Diplomatic-Entertainment/JustAnotherCartridgeReader/Firmware/FLASH_CPS3.ino

//******************************************
// CP System III Module
// Cartridge
// 32/64/128 Mbits SIMM
// Tested with  HW5
// https://github.com/herzmx/CPS3-OSCR-Adapter
//******************************************
#if (defined(ENABLE_CPS3) && defined(ENABLE_FLASH8) && defined(ENABLE_FLASH16))
/******************************************
   Variables
 *****************************************/
uint32_t cartRegion = 0;
uint32_t cartCD = 0;
uint32_t cartCDPatch = 0;
uint32_t multiCart = 0;
uint32_t multiCartPatch1 = 0;
uint32_t multiCartPatch2 = 0;
uint32_t cartRegionOffset = 0;
uint32_t cartnocdOffset = 0;
uint16_t flashids[8];

/******************************************
   Menu
 *****************************************/
// CPS3 start menu options
static const char cpsMenuItem1[] PROGMEM = "CPS3 cartridge";
static const char cpsMenuItem2[] PROGMEM = "32/128 Mbits SIMM";
static const char cpsMenuItem3[] PROGMEM = "64 Mbits SIMM";
static const char cpsMenuItem4[] PROGMEM = "32/128 MBytes SIMM";
static const char cpsMenuItem5[] PROGMEM = "64 MBytes SIMM";
static const char* const menuOptionsCPS[] PROGMEM = { cpsMenuItem1, cpsMenuItem2, cpsMenuItem3, cpsMenuItem4, cpsMenuItem5, FSTRING_RESET };

// Cartridge region options
static const char cpsCartRegion0[] PROGMEM = "No Patch";
static const char cpsCartRegion1[] PROGMEM = "JAP";
static const char cpsCartRegion2[] PROGMEM = "ASIA";
static const char cpsCartRegion3[] PROGMEM = "EUR";
static const char cpsCartRegion4[] PROGMEM = "USA";
static const char cpsCartRegion5[] PROGMEM = "HISPANIC";
static const char cpsCartRegion6[] PROGMEM = "BRAZIL";
static const char cpsCartRegion7[] PROGMEM = "OCEANIA";
static const char cpsCartRegion8[] PROGMEM = "ASIA NCD";
static const char* const menuOptionsCartRegion[] PROGMEM = { cpsCartRegion0, cpsCartRegion1, cpsCartRegion2, cpsCartRegion3, cpsCartRegion4, cpsCartRegion5, cpsCartRegion6, cpsCartRegion7, cpsCartRegion8, FSTRING_RESET };

// Cartridge cd options
static const char cpsCDItem1[] PROGMEM = "CD";
static const char cpsCDItem2[] PROGMEM = "NOCD";
static const char* const menuOptionsCartCD[] PROGMEM = { cpsCartRegion0, cpsCDItem1, cpsCDItem2, FSTRING_RESET };

// CPS3 start menu
void cpsMenu() {
  // create menu with title and 6 options to choose from
  unsigned char cpsType;
  convertPgm(menuOptionsCPS, 6);
  cpsType = question_box(FS(FSTRING_SELECT_CART_TYPE), menuOptions, 6, 0);

  // wait for user choice to come back from the question box menu
  switch (cpsType) {
    case 0:
      display_Clear();
      display_Update();
      mode = CORE_CPS3_CART;
      setup_CPS3();
      id_Flash8();
      wait();
      break;
    case 1:
      display_Clear();
      display_Update();
      mode = CORE_CPS3_128SIMM;
      setup_CPS3();
      id_SIMM2x8();
      wait();
      break;
    case 2:
      display_Clear();
      display_Update();
      mode = CORE_CPS3_64SIMM;
      setup_CPS3();
      id_SIMM4x8();
      wait();
      break;
    case 3:
      display_Clear();
      display_Update();
      mode = CORE_CPS3_01SIMM;
      setup_CPS3();
      break;
    case 4:
      display_Clear();
      display_Update();
      mode = CORE_CPS3_512SIMM;
      setup_CPS3();
      break;
    case 5:
      resetArduino();
      break;
    default:
      print_MissingModule();  // does not return
  }
}

// CPS3 Cartridge menu
void flashromCPS_Cartridge() {
  // create menu with title and 7 options to choose from
  unsigned char mainMenu;
  // Copy menuOptions out of progmem
  convertPgm(menuOptionsFLASH8, 7);
  mainMenu = question_box(F("CPS3 Cartdrige Writer"), menuOptions, 7, 0);

  // wait for user choice to come back from the question box menu
  switch (mainMenu) {
    case 0:
      display_Clear();
      println_Msg(F("Blankcheck"));
      display_Update();
      time = millis();
      resetFlash8();
      blankcheck_Flash();
      break;

    case 1:
      if (flashromType != 0) {
        display_Clear();
        println_Msg(F("Warning: This will erase"));
        println_Msg(F("your CPS3 Cartdrige BIOS"));
        print_STR(press_button_STR, 1);
        display_Update();
        wait();
        rgbLed(black_color);
        println_Msg(FS(FSTRING_EMPTY));
        println_Msg(F("Please wait..."));
        display_Update();
        time = millis();

        switch (flashromType) {
          case 1: eraseFlash29F032(); break;
          case 2: eraseFlash29F1610(); break;
          case 3: eraseFlash28FXXX(); break;
        }

        println_Msg(F("CPS3 Cartdrige BIOS erased"));
        display_Update();
        resetFlash8();
      } else {
        readOnlyMode();
      }
      break;

    case 2:
      time = millis();
      resetFlash8();
      readCartridge();
      break;

    case 3:
      if (flashromType != 0) {
        // Set cartridge region
        filePath[0] = '\0';
        sd.chdir("/");
        fileBrowser(FS(FSTRING_SELECT_FILE));
        // Calculate CRC32 of BIOS
        display_Clear();
        println_Msg("Looking BIOS patch");
        println_Msg(FS(FSTRING_EMPTY));
        println_Msg(F("Please wait..."));
        display_Update();
        char crcStr[9];
        sprintf(crcStr, "%08lX", calculateCRC(fileName, filePath, 0));
        setCartridgePatchData(crcStr);
        display_Clear();
        time = millis();

        switch (flashromType) {
          case 1:
            break;
          case 2:
            if ((flashid == 0x0458) || (flashid == 0x0158) || (flashid == 0x01AB) || (flashid == 0x0422) || (flashid == 0x0423))
              writeCartridge();
            else if (flashid == 0x0)  // Manual flash config, pick most common type
              writeFlash29LV640();
            break;
          case 3:
            break;
        }

        delay(100);

        // Reset twice just to be sure
        resetFlash8();
        resetFlash8();

        verifyCartridge();
      } else {
        readOnlyMode();
      }
      break;

    case 4:
      time = 0;
      display_Clear();
      resetFlash8();
      println_Msg(F("ID Flashrom"));
      switch (flashromType) {
        case 0: break;
        case 1: idFlash29F032(); break;
        case 2: idFlash29F1610(); break;
        case 3: idFlash28FXXX(); break;
      }
      println_Msg(FS(FSTRING_EMPTY));
      printFlash(40);
      println_Msg(FS(FSTRING_EMPTY));
      display_Update();
      resetFlash8();
      break;

    case 5:
      time = 0;
      display_Clear();
      println_Msg(F("Print first 70Bytes"));
      display_Update();
      resetFlash8();
      printFlash(70);
      break;

    case 6:
      time = 0;
      display_Clear();
      display_Update();
      resetFlash8();
      resetArduino();
      break;
  }
  if (time != 0) {
    print_Msg(F("Operation took : "));
    print_Msg((millis() - time) / 1000, DEC);
    println_Msg(F("s"));
    display_Update();
  }
  // Prints string out of the common strings array either with or without newline
  print_STR(press_button_STR, 0);
  display_Update();
  wait();
}

// CPS3 Cartridge region patch menu
void cpsCartRegionMenu() {
  cartRegion = pageMenu(F("Cartridge Region Patch"), menuOptionsCartRegion, 10);
  if (cartRegion < 9) {
    display_Clear();
    display_Update();
  } else {
    time = 0;
    display_Clear();
    display_Update();
    resetFlash8();
    resetArduino();
  }
}

// CPS3 Cartridge CD patch menu
void cpsCartCDMenu() {
  // Copy menuOptions out of progmem
  convertPgm(menuOptionsCartCD, 4);
  cartCD = question_box(F("Cartridge CD Patch"), menuOptions, 4, 0);

  // wait for user choice to come back from the question box menu
  if (cartCD < 3) {
    display_Clear();
    display_Update();
  } else {
    time = 0;
    display_Clear();
    display_Update();
    resetFlash8();
    resetArduino();
  }
}

// CPS3 32/128 SIMM menu
void flashromCPS_SIMM2x8() {
  // create menu with title and 7 options to choose from
  unsigned char mainMenu;
  // Copy menuOptions out of progmem
  convertPgm(menuOptionsFLASH8, 7);
  mainMenu = question_box(F("CPS3 SIMM Writer 2x8bit"), menuOptions, 7, 0);

  // wait for user choice to come back from the question box menu
  switch (mainMenu) {
    case 0:
      display_Clear();
      println_Msg(F("Blankcheck"));
      display_Update();
      time = millis();
      resetSIMM2x8();
      blankcheckSIMM2x8();
      break;

    case 1:
      if (flashromType != 0) {
        display_Clear();
        println_Msg(F("Warning: This will erase"));
        println_Msg(F("your CPS3 SIMM 2x8bit"));
        print_STR(press_button_STR, 1);
        display_Update();
        wait();
        rgbLed(black_color);
        println_Msg(FS(FSTRING_EMPTY));
        println_Msg(F("Please wait..."));
        display_Update();
        time = millis();

        switch (flashromType) {
          case 1: eraseSIMM2x8(); break;
          case 2: break;
          case 3: break;
        }

        println_Msg(F("CPS3 SIMM 2x8bit erased"));
        display_Update();
        resetSIMM2x8();
      } else {
        readOnlyMode();
      }
      break;

    case 2:
      time = millis();
      resetSIMM2x8();
      readSIMM2x8B();
      break;

    case 3:
      if (flashromType != 0) {
        // Set cartridge region
        filePath[0] = '\0';
        sd.chdir("/");
        fileBrowser(FS(FSTRING_SELECT_FILE));
        display_Clear();
        time = millis();

        switch (flashromType) {
          case 1:
            if (flashid == 0x04AD)
              writeSIMM2x8();
            break;
          case 2:
            break;
          case 3:
            break;
        }

        delay(100);

        // Reset twice just to be sure
        resetSIMM2x8();
        resetSIMM2x8();

        verifySIMM2x8();
      } else {
        readOnlyMode();
      }
      break;

    case 4:
      time = 0;
      display_Clear();
      resetFlash8();
      println_Msg(F("ID Flashrom"));
      switch (flashromType) {
        case 0: break;
        case 1: idFlash2x8(0x0); break;
        case 2: break;
        case 3: break;
      }
      println_Msg(FS(FSTRING_EMPTY));
      printFlash16(40);
      println_Msg(FS(FSTRING_EMPTY));
      display_Update();
      resetSIMM2x8();
      break;

    case 5:
      time = 0;
      display_Clear();
      println_Msg(F("Print first 70Bytes"));
      display_Update();
      resetSIMM2x8();
      printFlash16(70);
      break;

    case 6:
      time = 0;
      display_Clear();
      display_Update();
      resetSIMM2x8();
      resetArduino();
      break;
  }
  if (time != 0) {
    print_Msg(F("Operation took : "));
    print_Msg((millis() - time) / 1000, DEC);
    println_Msg(F("s"));
    display_Update();
  }
  // Prints string out of the common strings array either with or without newline
  print_STR(press_button_STR, 0);
  display_Update();
  wait();
}

// CPS3 32/128 SIMM menu
void flashromCPS_SIMM4x8() {
  // create menu with title and 7 options to choose from
  unsigned char mainMenu;
  // Copy menuOptions out of progmem
  convertPgm(menuOptionsFLASH8, 7);
  mainMenu = question_box(F("CPS3 SIMM Writer 4x8bit"), menuOptions, 7, 0);

  // wait for user choice to come back from the question box menu
  switch (mainMenu) {
    case 0:
      display_Clear();
      println_Msg(F("Blankcheck"));
      display_Update();
      time = millis();
      resetSIMM4x8();
      blankcheckSIMM4x8();
      break;

    case 1:
      if (flashromType != 0) {
        display_Clear();
        println_Msg(F("Warning: This will erase"));
        println_Msg(F("your CPS3 SIMM 4x8bit"));
        print_STR(press_button_STR, 1);
        display_Update();
        wait();
        rgbLed(black_color);
        println_Msg(FS(FSTRING_EMPTY));
        println_Msg(F("Please wait..."));
        display_Update();
        time = millis();

        switch (flashromType) {
          case 1: eraseSIMM4x8(); break;
          case 2: break;
          case 3: break;
        }

        println_Msg(F("CPS3 SIMM 4x8bit erased"));
        display_Update();
        resetSIMM4x8();
      } else {
        readOnlyMode();
      }
      break;

    case 2:
      time = millis();
      resetSIMM4x8();
      readSIMM4x8();
      break;

    case 3:
      if (flashromType != 0) {
        // Set cartridge region
        filePath[0] = '\0';
        sd.chdir("/");
        fileBrowser(FS(FSTRING_SELECT_FILE));
        display_Clear();
        time = millis();

        switch (flashromType) {
          case 1:
            if (flashid == 0x04AD)
              writeSIMM4x8();
            break;
          case 2:
            break;
          case 3:
            break;
        }

        delay(100);

        // Reset twice just to be sure
        resetSIMM4x8();
        resetSIMM4x8();

        verifySIMM4x8();
      } else {
        readOnlyMode();
      }
      break;

    case 4:
      time = 0;
      display_Clear();
      resetFlash8();
      println_Msg(F("ID Flashrom"));
      switch (flashromType) {
        case 0: break;
        case 1:
          enable64MSB();
          idFlash2x8(0x0);
          enable64LSB();
          idFlash2x8(0x1);
          break;
        case 2: break;
        case 3: break;
      }
      println_Msg(FS(FSTRING_EMPTY));
      printSIMM4x8(40);
      println_Msg(FS(FSTRING_EMPTY));
      display_Update();
      resetSIMM4x8();
      break;

    case 5:
      time = 0;
      display_Clear();
      println_Msg(F("Print first 70Bytes"));
      display_Update();
      resetSIMM4x8();
      enable64MSB();
      printSIMM4x8(70);
      break;

    case 6:
      time = 0;
      display_Clear();
      display_Update();
      resetSIMM4x8();
      resetArduino();
      break;
  }
  if (time != 0) {
    print_Msg(F("Operation took : "));
    print_Msg((millis() - time) / 1000, DEC);
    println_Msg(F("s"));
    display_Update();
  }
  // Prints string out of the common strings array either with or without newline
  print_STR(press_button_STR, 0);
  display_Update();
  wait();
}

/******************************************
   Setup
 *****************************************/
void setup_CPS3() {
  // Set Address Pins to Output
  //A0-A7
  DDRF = 0xFF;
  //A8-A15
  DDRK = 0xFF;
  //A16-A23
  DDRL = 0xFF;
  //A24(PJ0), A25(PJ1)
  DDRJ |= (1 << 0) | (1 << 1);

  // Set Control Pins to Output
  // RST(PH0) OE(PH1) BYTE(PH3) WE(PH4) CKIO_CPU(PH5) CE/CER_CST(PH6)
  DDRH |= (1 << 0) | (1 << 1) | (1 << 3) | (1 << 4) | (1 << 5) | (1 << 6);
  // CE64LSB(PE3) CE128(PE4)
  DDRE |= (1 << 3) | (1 << 4);
  // RST_CPUC(PG1) CE64MSB(PG5)
  DDRG |= (1 << 1) | (1 << 5);

  // Set Data Pins (D0-D15) to Input
  DDRC = 0x00;
  DDRA = 0x00;
  // Disable Internal Pullups
  PORTC = 0x00;
  PORTA = 0x00;

  // Setting RST(PH0) OE(PH1) WE(PH4) CKIO_CPU(PH5) HIGH
  PORTH |= (1 << 0) | (1 << 1) | (1 << 4) | (1 << 5);
  // Setting CE64LSB(PE3) CE128(PE4) HIGH
  PORTE |= (1 << 3) | (1 << 4);
  // Setting CE64MSB(PG5) HIGH
  PORTG |= (1 << 5);
  // Setting CE_CART/CER_CST(PH6) HIGH
  PORTH |= (1 << 6);
  // Setting BYTE(PH3) LOW
  PORTH &= ~(1 << 3);
  // Setting RST_CPUC(PG1) LOW
  PORTG &= ~(1 << 1);

  if (mode == CORE_CPS3_128SIMM || mode == CORE_CPS3_01SIMM) {
    // Setting CE128(PE4) LOW
    PORTE &= ~(1 << 4);
  } else if (mode == CORE_CPS3_CART) {
    // Setting CE_CART/CER_CST(PH6) LOW
    PORTH &= ~(1 << 6);
  }

  byteCtrl = 1;
}

/******************************************
   Low level functions
 *****************************************/
void enable64MSB() {
  // Setting CE64LSB(PE3) HIGH
  PORTE |= (1 << 3);
  // Setting CE64MSB(PG5) LOW
  PORTG &= ~(1 << 5);
  // Wait till output is stable
  NOP;
  NOP;
}
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
